hydronics2/Circuitpython_February_2019/programming/pics/a2_accelerometer_code2.JPG

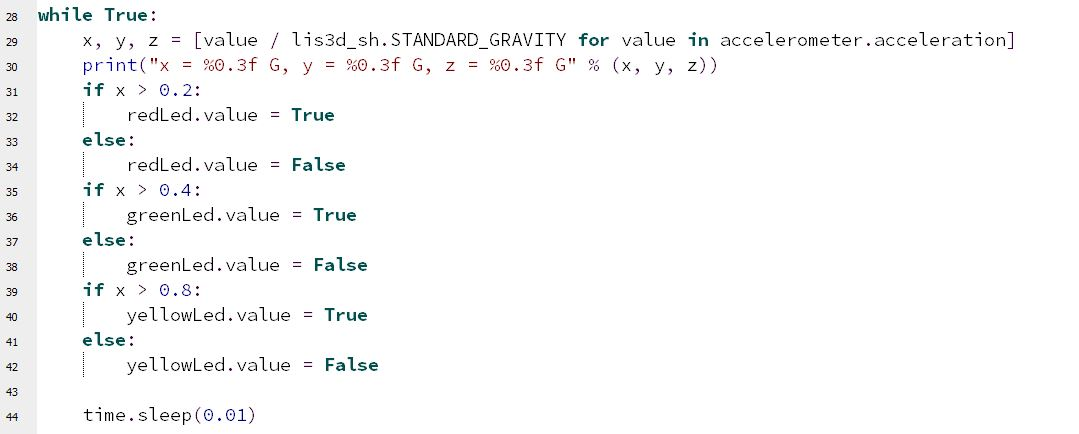
programming/pics/a2_accelerometer_code2.JPG
