hydronics2/Circuitpython_February_2019/programming/pics/photocell.JPG

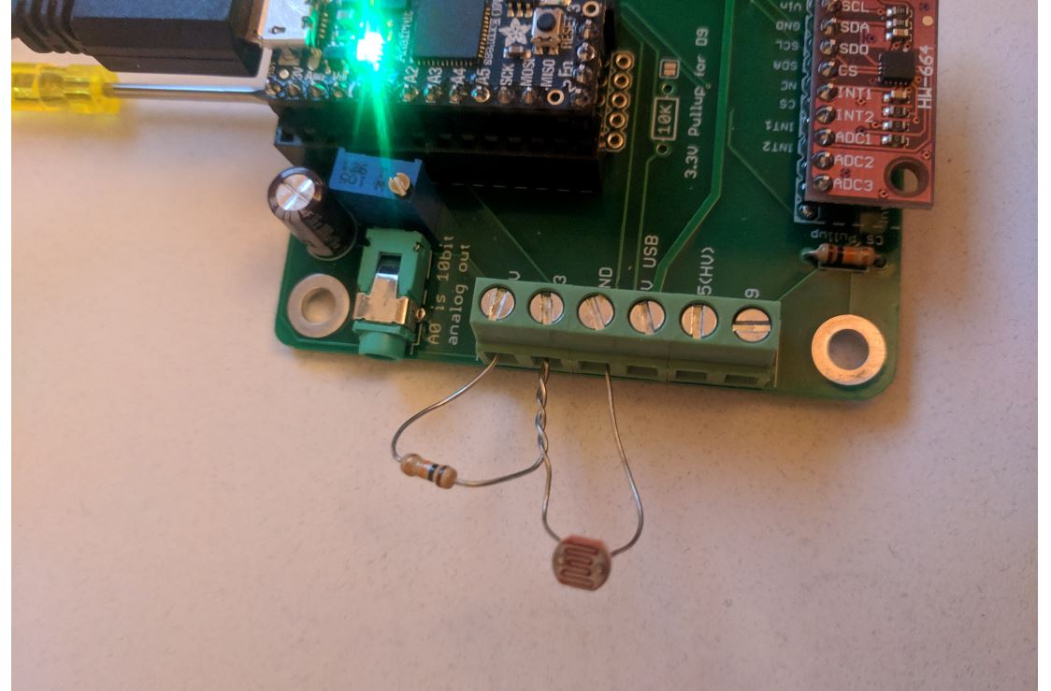
programming/pics/photocell.JPG
