hydronics2/Circuitpython_February_2019/programming/python_files/code.py

# this is code.py. Code.py is the first script to execute.... so whatever is here will run

# see below all the python scripts. remove the '#' one at a time to run the script.
# they start with a1,a2,a3 because python doesn't like files starting with numbers: 1_, 2_


import a1_blink_digital_out_example
#import a2_accelerometer_led
#import a3_play_wav_file
#import a4_ws2812_example

#import digital_input_example 
#import pwm_example
#import analog_in_example
#import accelerometer_wav
#import play_tone


 
